golioth/phial-hw/input/art/JLC06081H-2116.png

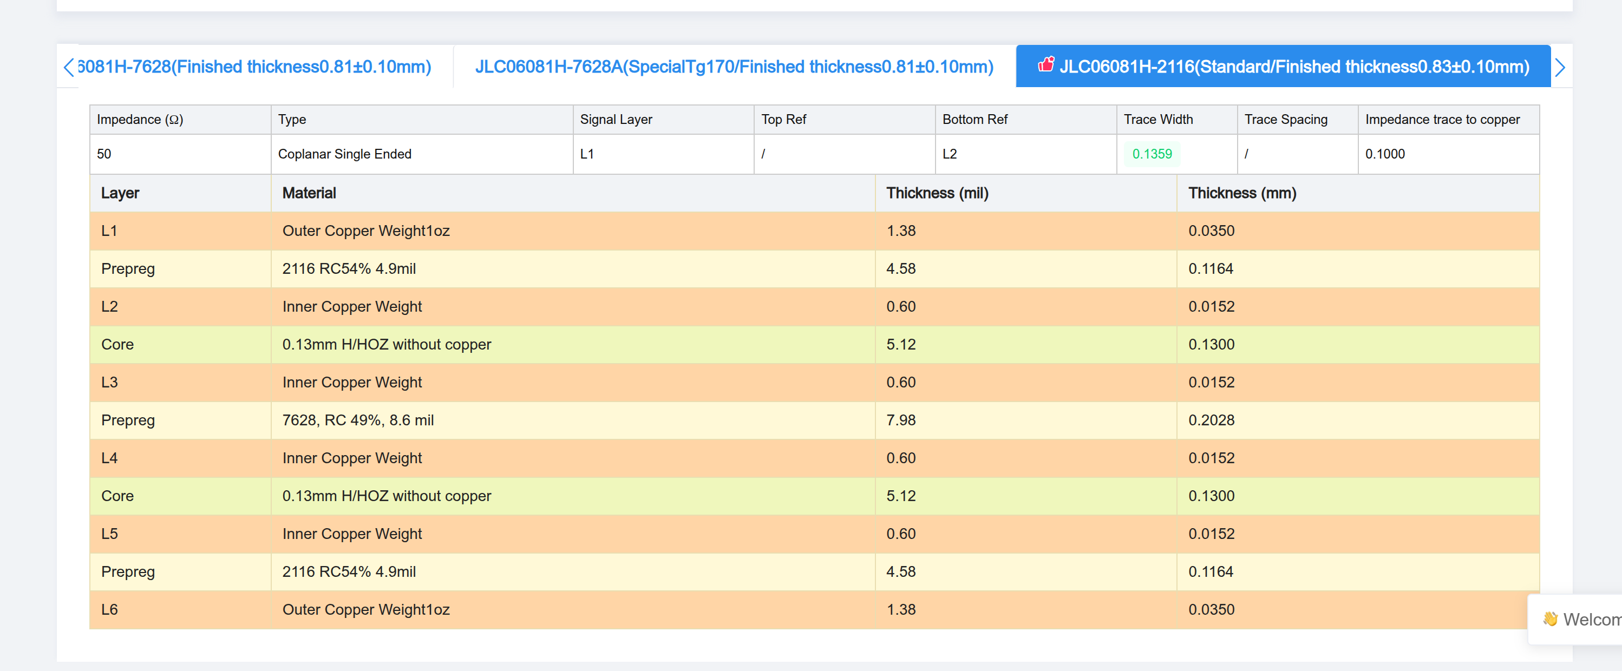
input/art/JLC06081H-2116.png
