golioth/phial-hw/input/art/nRF54L15-QFAA-reference.png

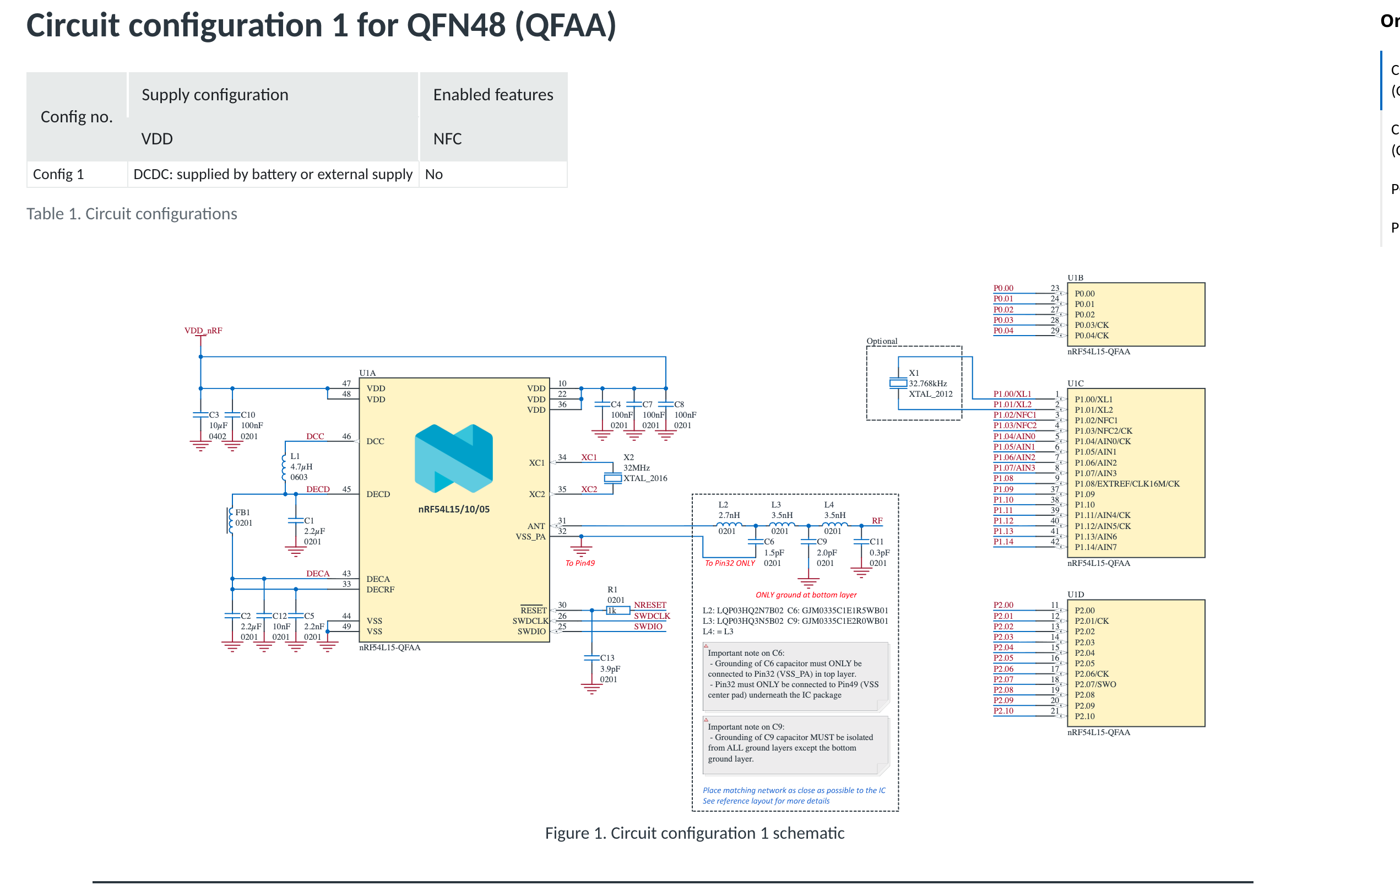
input/art/nRF54L15-QFAA-reference.png
