golioth/phial-hw/input/art/nrf54L15-reference.png

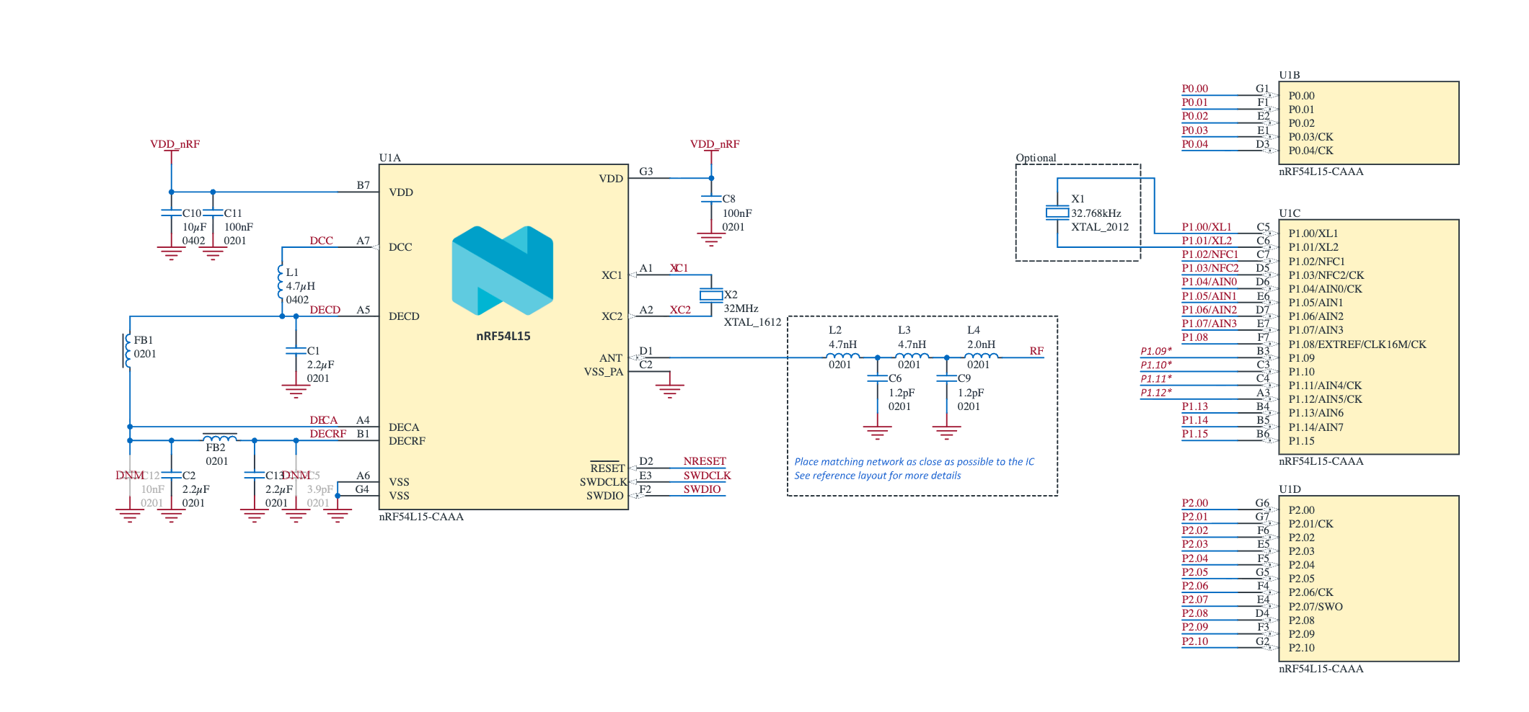
input/art/nrf54L15-reference.png
