golioth/phial-hw/input/art/orleon_6mm.png

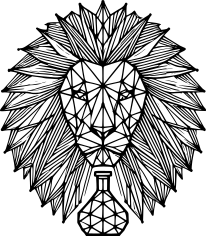
input/art/orleon_6mm.png
