golioth/phial-hw/input/art/Pilulith.png

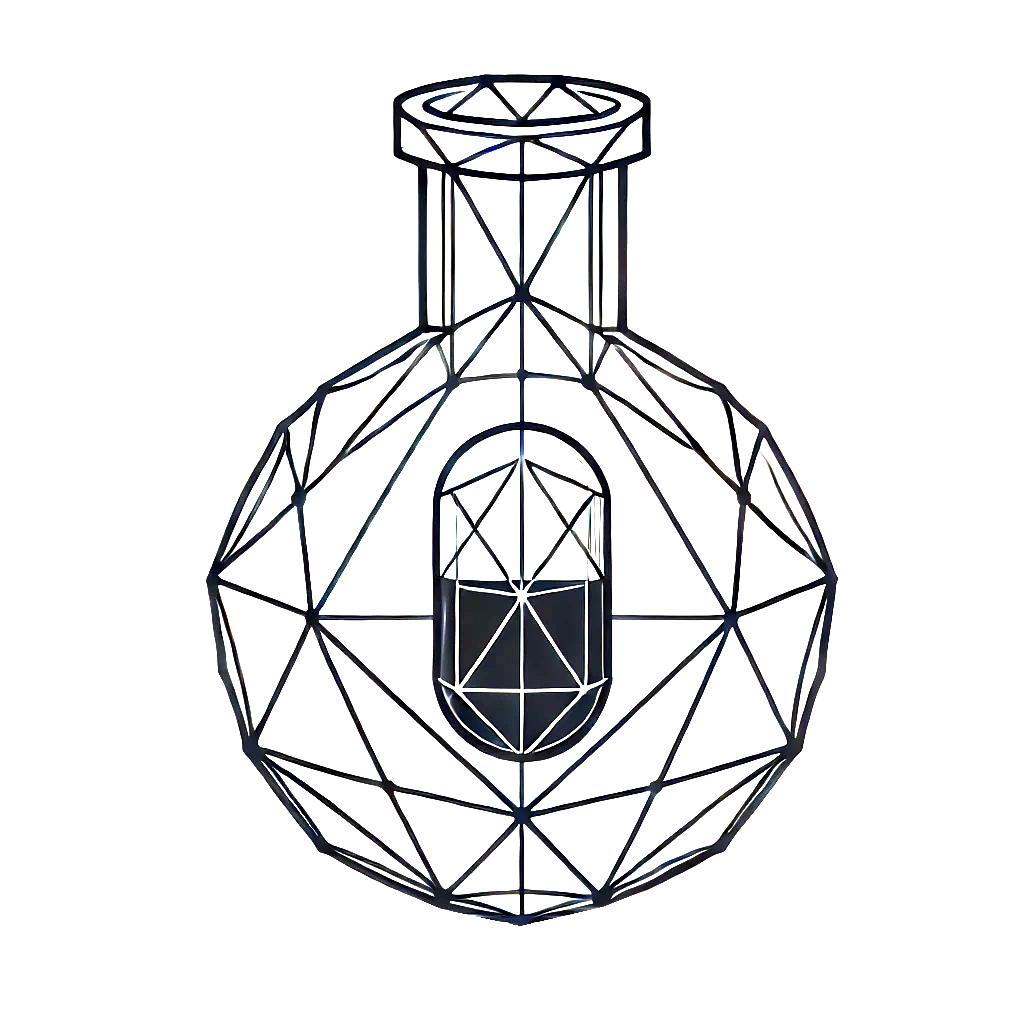
input/art/Pilulith.png
