golioth/phial-hw/input/art/WLA-04-Dimensions.png

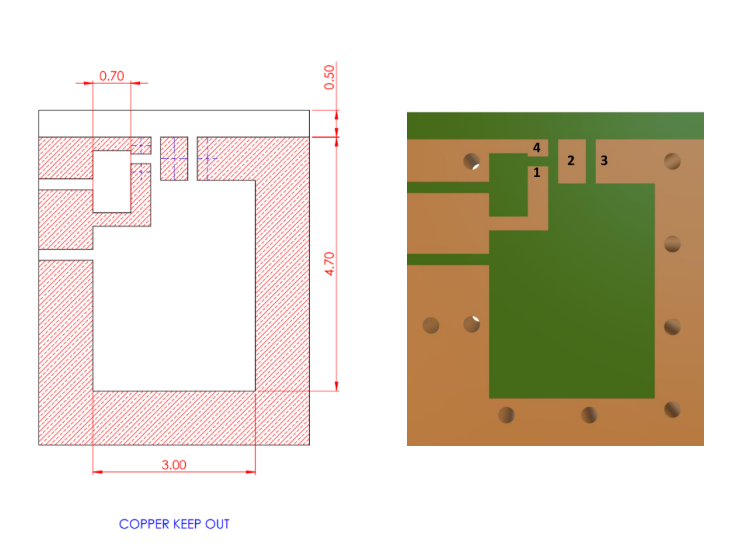
input/art/WLA-04-Dimensions.png
