golioth/phial-hw/input/3d/NRF52840-CKAA-F-R.step

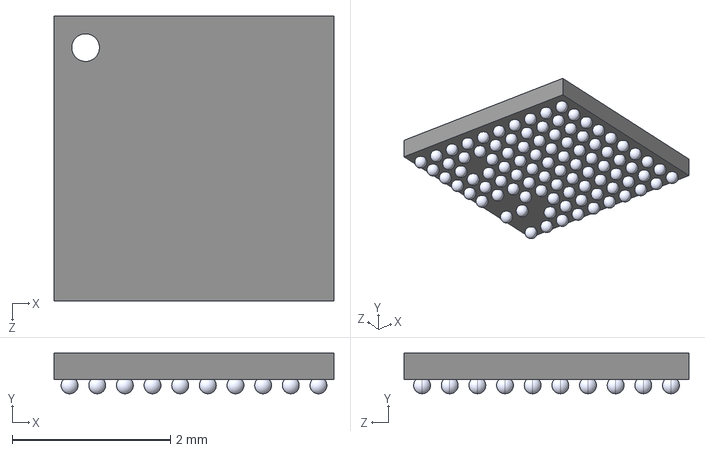
[picture p26: CAD file, 2025-03-07]
input/3d/NRF52840-CKAA-F-R.step
3.54 x 0.514 x 3.61 mm
